Riesi/ploopy_mouse_kicad/gerber_diff_validation/layer_1_diff.png

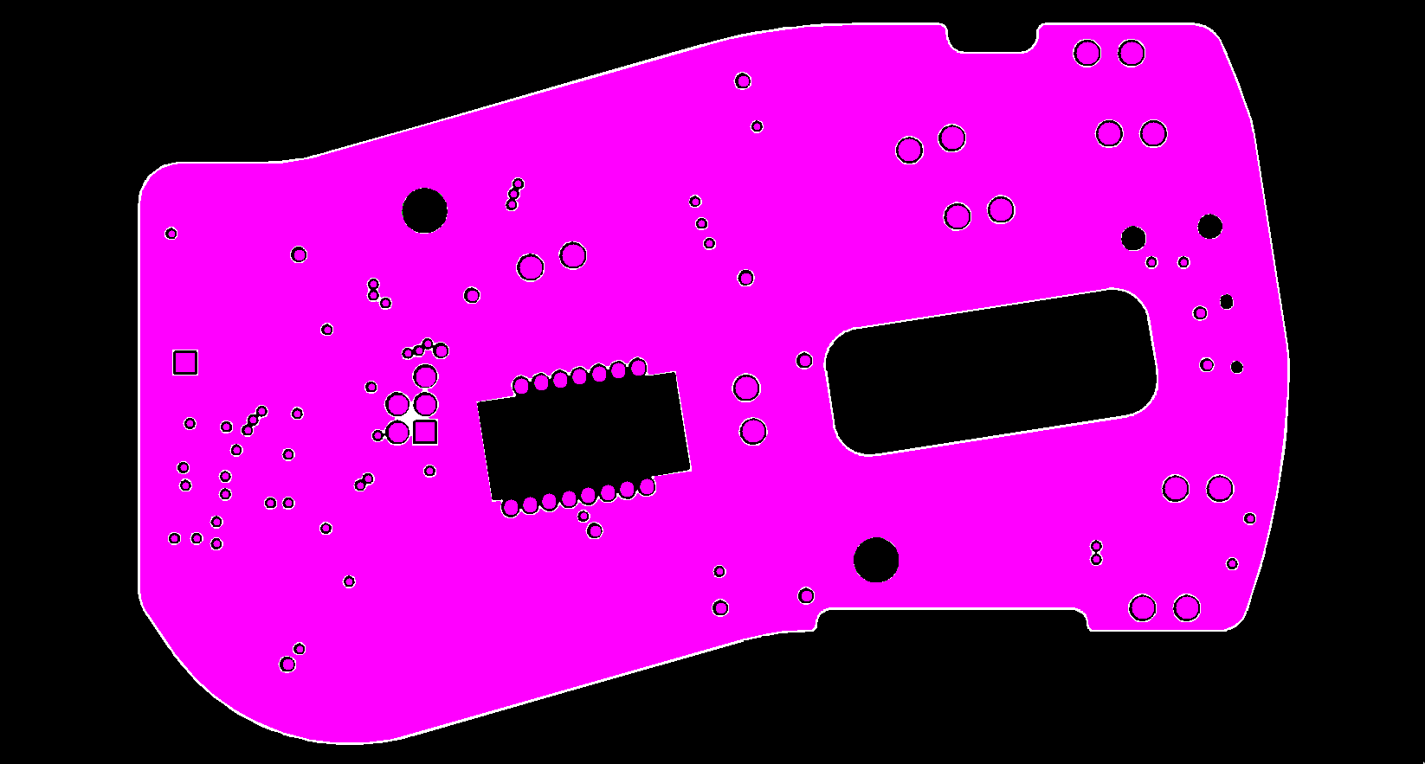
gerber_diff_validation/layer_1_diff.png
